3dfernando/ESP16_Connector/Pictures/PXL_20210929_192935468.jpg

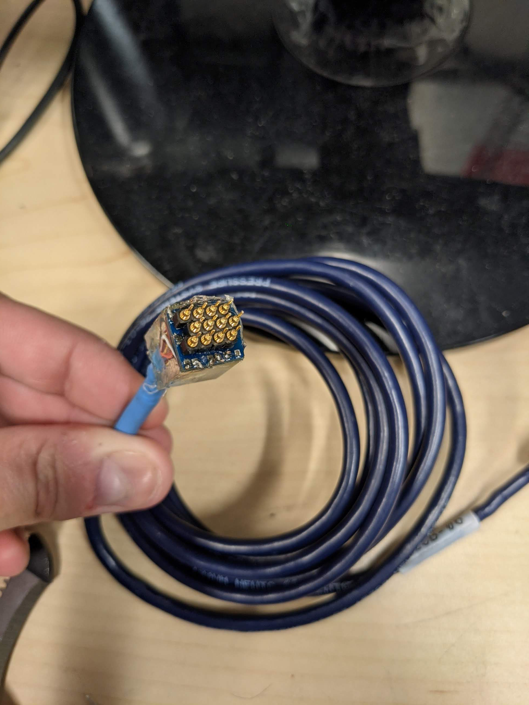
Pictures/PXL_20210929_192935468.jpg
